golaced/Quadruped-Robot-Moco-12-/教程2-主机架设计/moco-8 Test Verison/侧摆电机.SLDPRT

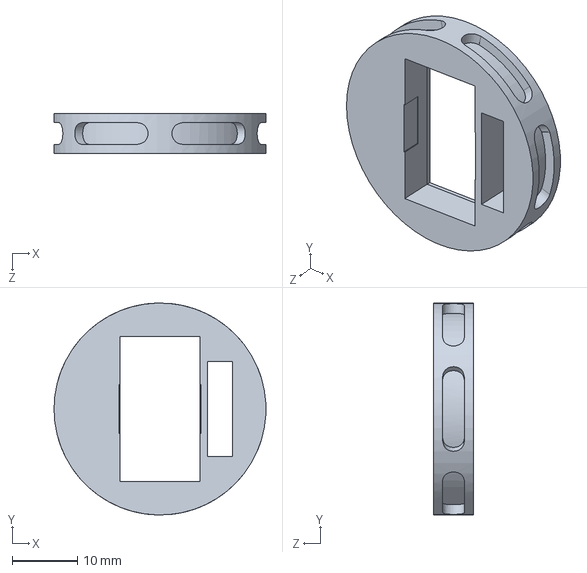
[picture p118: CAD file, 2020-06-26]
教程2-主机架设计/moco-8 Test Verison/侧摆电机.SLDPRT
32.5 x 32.5 x 6.13 mm
