golaced/Quadruped-Robot-Moco-12-/教程2-主机架设计/1.0 SW文件/开关支撑.SLDPRT

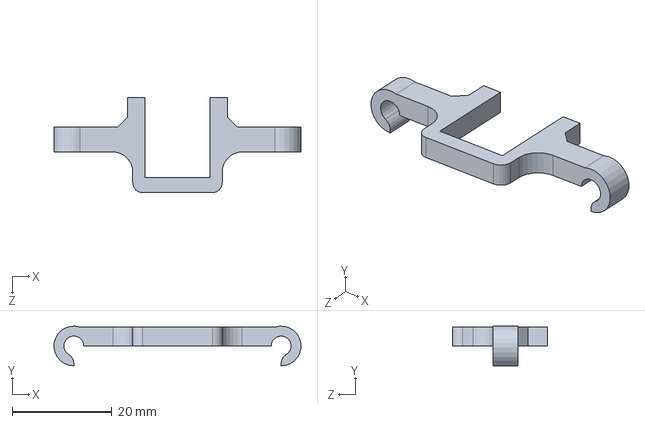
[picture p119: CAD file, 2020-02-27]
教程2-主机架设计/1.0 SW文件/开关支撑.SLDPRT
49.6 x 7.99 x 19.2 mm
