golaced/Quadruped-Robot-Moco-12-/教程2-主机架设计/1.2 版本加工文件/小腿杆 4个.SLDPRT

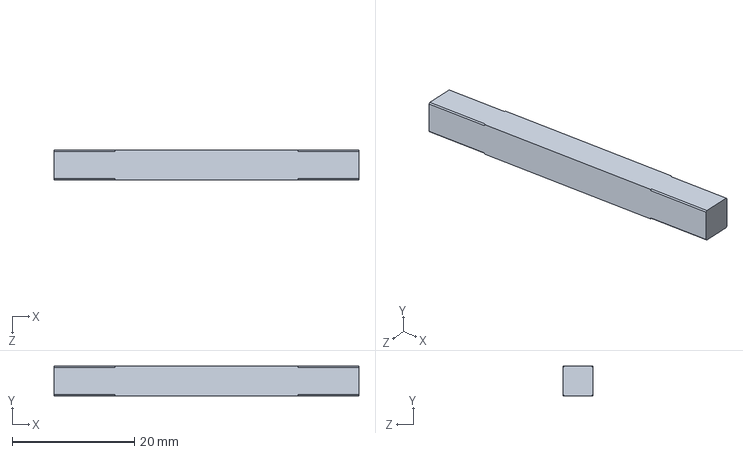
[picture p120: CAD file, 2020-06-15]
教程2-主机架设计/1.2 版本加工文件/小腿杆 4个.SLDPRT
50.0 x 4.85 x 4.85 mm
