golaced/Quadruped-Robot-Moco-12-/教程2-主机架设计/moco-8 Test Verison/大腿.SLDPRT

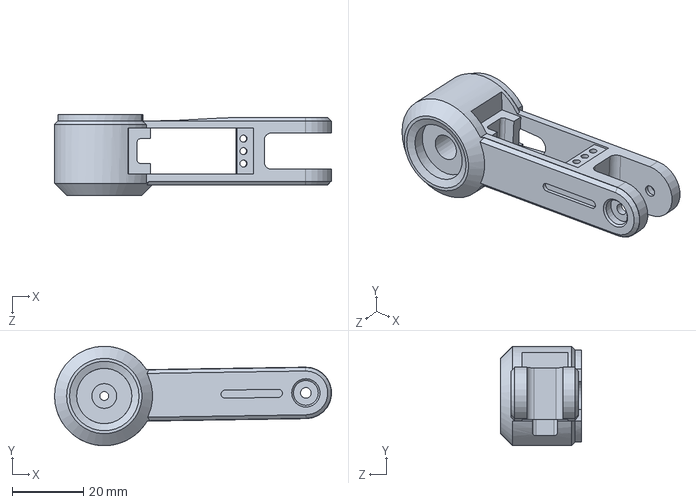
[picture p121: CAD file, 2020-06-26]
教程2-主机架设计/moco-8 Test Verison/大腿.SLDPRT
77.9 x 28.0 x 22.8 mm
