golaced/Quadruped-Robot-Moco-12-/教程2-主机架设计/1.0 SW文件/大腿_舵机保护.SLDPRT

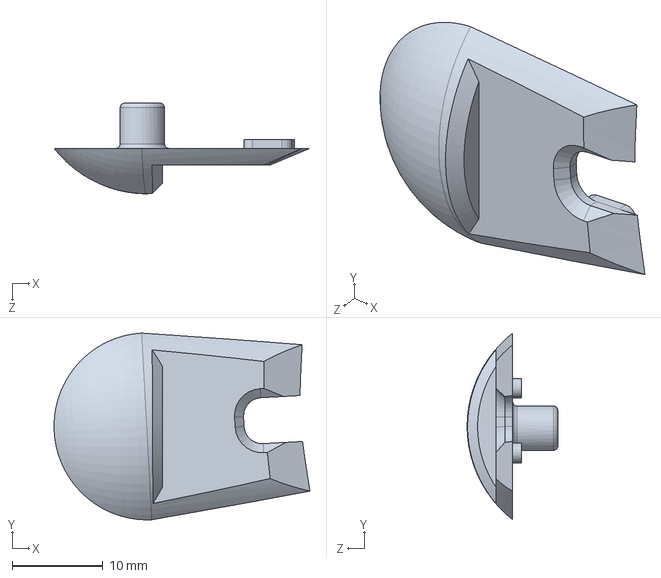
[picture p122: CAD file, 2020-02-27]
教程2-主机架设计/1.0 SW文件/大腿_舵机保护.SLDPRT
28.3 x 20.6 x 10.0 mm
