golaced/Quadruped-Robot-Moco-12-/教程2-主机架设计/moco-8 Test Verison/足底.SLDPRT

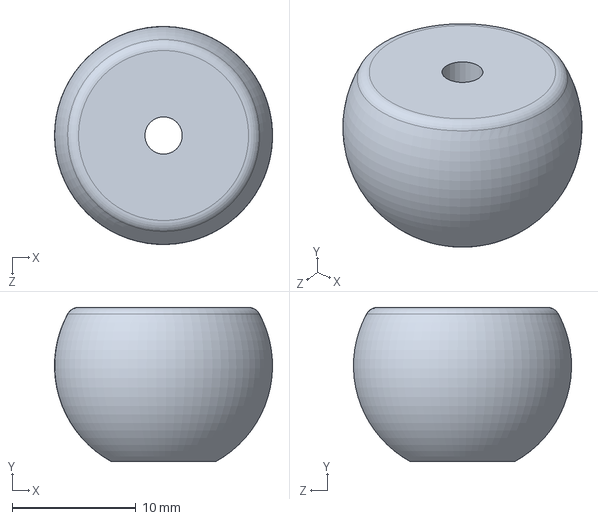
[picture p123: CAD file, 2020-06-26]
教程2-主机架设计/moco-8 Test Verison/足底.SLDPRT
17.6 x 12.4 x 17.6 mm
