golaced/Quadruped-Robot-Moco-12-/教程2-主机架设计/1.2 版本加工文件/侧挡板1 2个.SLDPRT

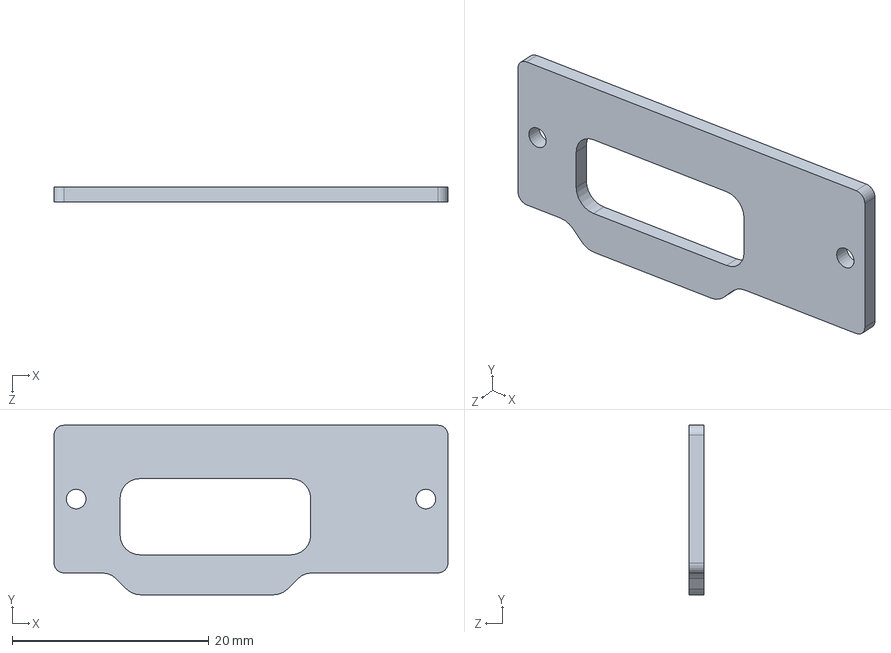
[picture p124: CAD file, 2020-06-15]
教程2-主机架设计/1.2 版本加工文件/侧挡板1 2个.SLDPRT
40.0 x 17.2 x 1.50 mm
