golaced/Quadruped-Robot-Moco-12-/教程2-主机架设计/1.0 SW文件/顶支架.SLDPRT

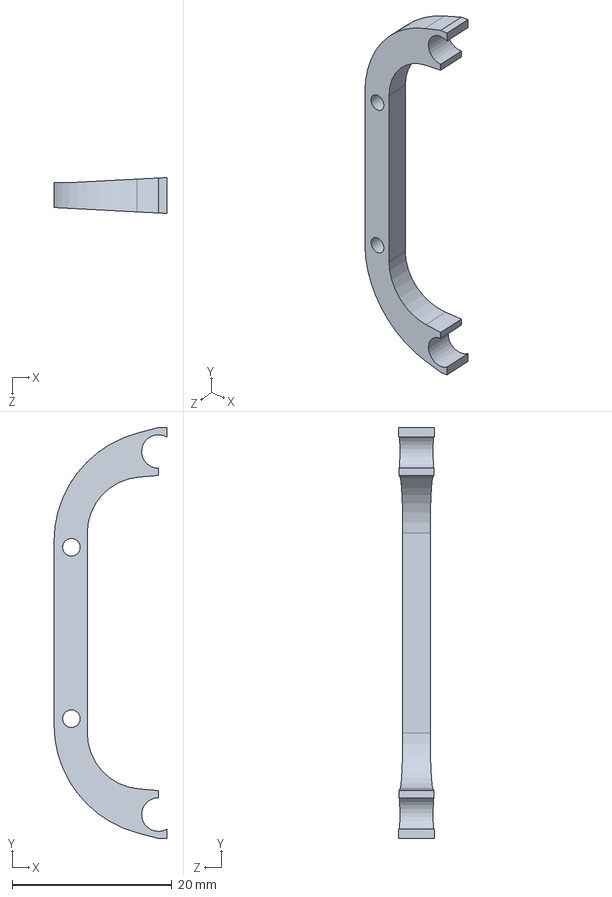
[picture p125: CAD file, 2020-02-27]
教程2-主机架设计/1.0 SW文件/顶支架.SLDPRT
14.1 x 51.5 x 4.50 mm
