golaced/Quadruped-Robot-Moco-12-/教程2-主机架设计/1.2 版本加工文件/侧挡板2 2个.SLDPRT

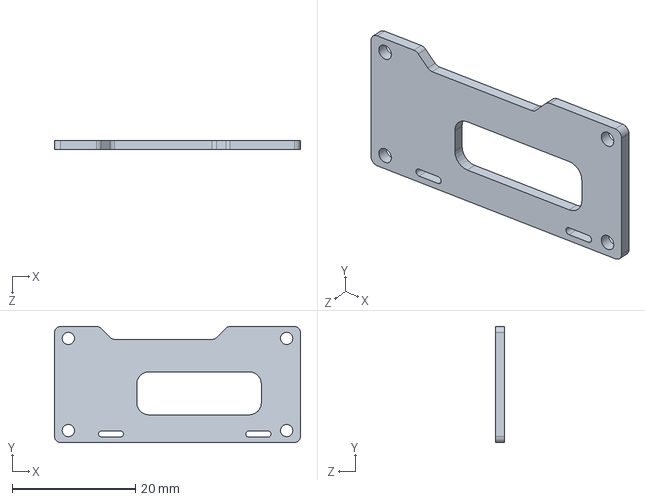
[picture p126: CAD file, 2020-06-15]
教程2-主机架设计/1.2 版本加工文件/侧挡板2 2个.SLDPRT
40.0 x 18.9 x 1.50 mm
