golaced/Quadruped-Robot-Moco-12-/教程2-主机架设计/1.0 SW文件/电池仓.SLDPRT

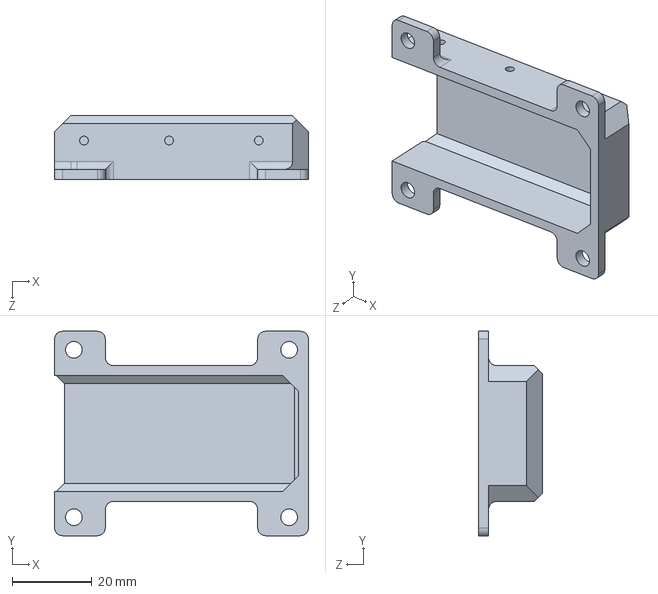
[picture p127: CAD file, 2020-02-27]
教程2-主机架设计/1.0 SW文件/电池仓.SLDPRT
63.7 x 51.3 x 16.0 mm
