golaced/Quadruped-Robot-Moco-12-/教程2-主机架设计/1.2 版本加工文件/控制器安装结构件 1个.SLDPRT

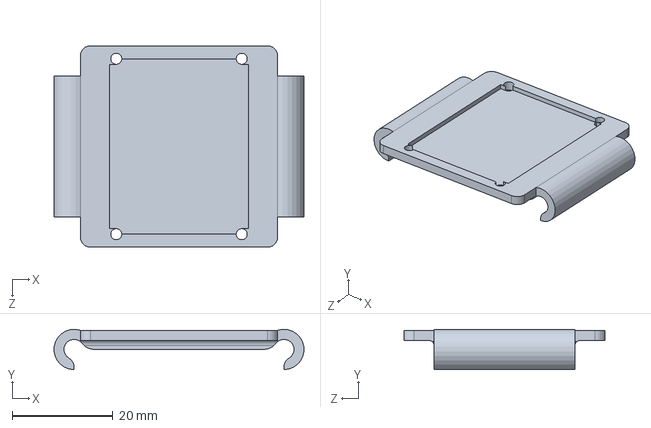
[picture p128: CAD file, 2020-06-15]
教程2-主机架设计/1.2 版本加工文件/控制器安装结构件 1个.SLDPRT
49.6 x 7.99 x 40.0 mm
