golaced/Quadruped-Robot-Moco-12-/教程2-主机架设计/moco-8 Test Verison/顶盖.SLDPRT

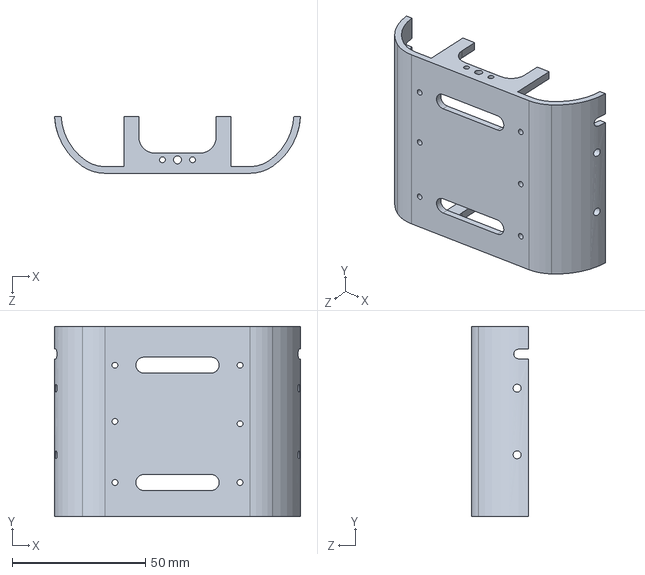
[picture p129: CAD file, 2020-06-26]
教程2-主机架设计/moco-8 Test Verison/顶盖.SLDPRT
92.3 x 71.4 x 21.2 mm
