golaced/Quadruped-Robot-Moco-12-/教程2-主机架设计/1.0 SW文件/跨舵机固定双.SLDPRT

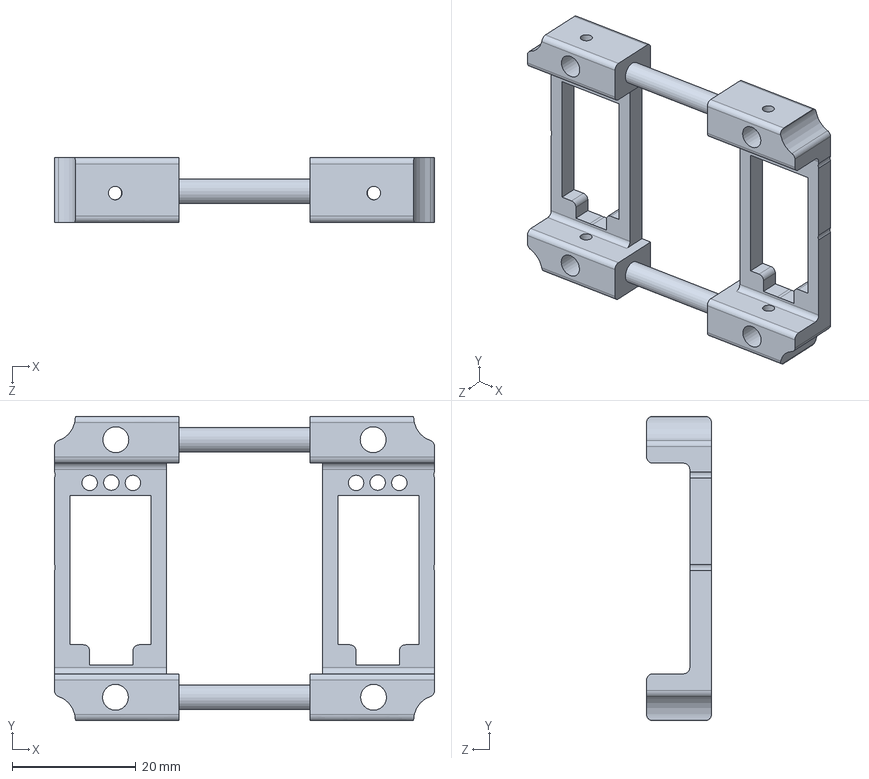
[picture p130: CAD file, 2020-02-27]
教程2-主机架设计/1.0 SW文件/跨舵机固定双.SLDPRT
61.5 x 49.3 x 10.5 mm
