golaced/Quadruped-Robot-Moco-12-/教程2-主机架设计/1.2 版本加工文件/顶部把手 2个.SLDPRT

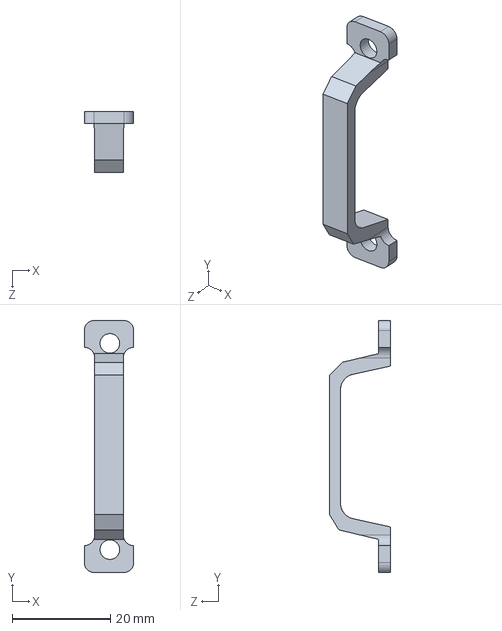
[picture p131: CAD file, 2020-06-15]
教程2-主机架设计/1.2 版本加工文件/顶部把手 2个.SLDPRT
10.1 x 51.3 x 12.5 mm
