golaced/Quadruped-Robot-Moco-12-/教程2-主机架设计/moco-8 Test Verison/小腿.SLDPRT

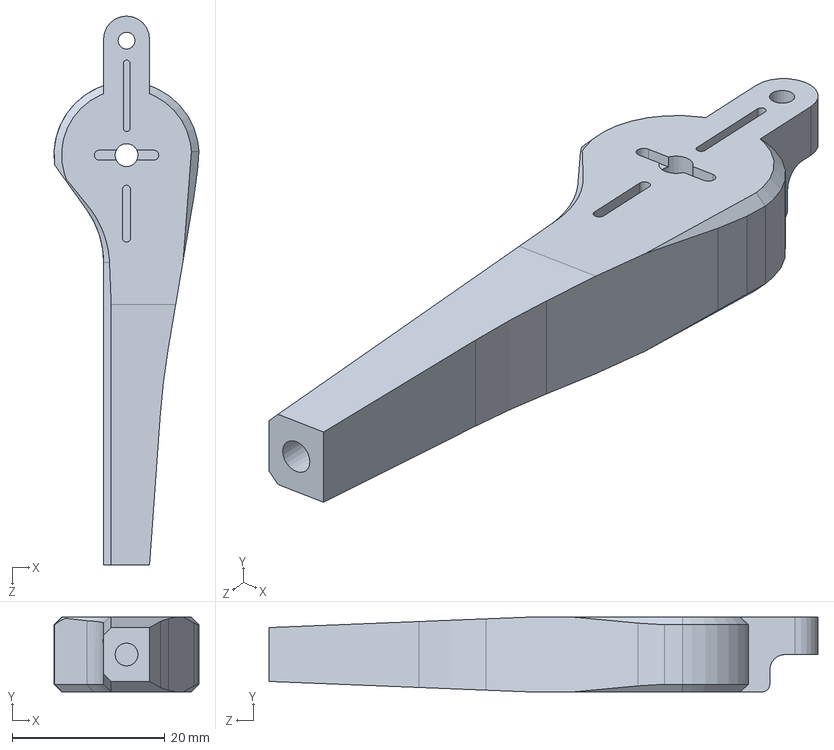
[picture p132: CAD file, 2020-06-26]
教程2-主机架设计/moco-8 Test Verison/小腿.SLDPRT
19.0 x 9.80 x 71.9 mm
