golaced/Quadruped-Robot-Moco-12-/教程2-主机架设计/1.2 版本加工文件/侧摆电机固定件 4个.SLDPRT

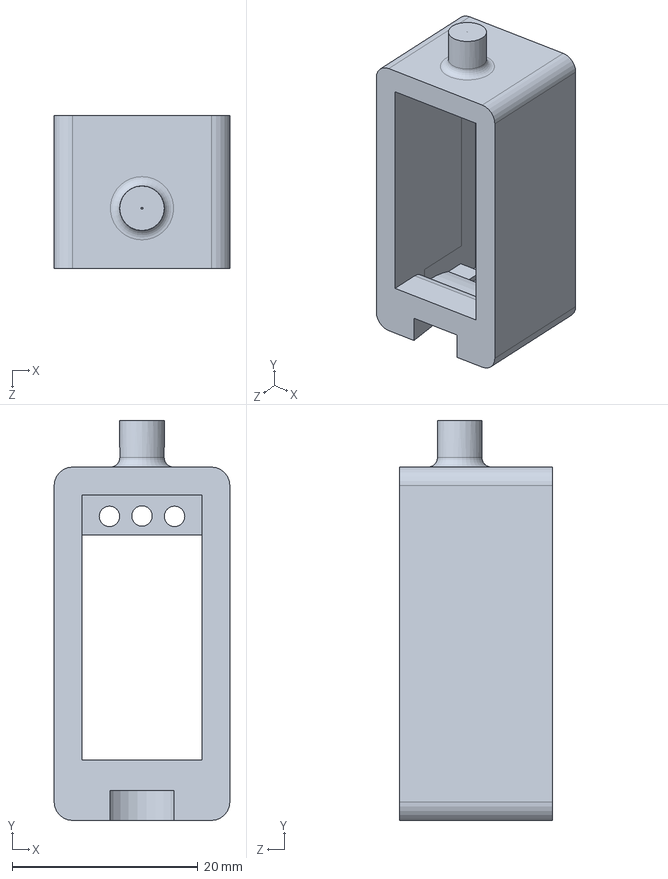
[picture p133: CAD file, 2020-06-15]
教程2-主机架设计/1.2 版本加工文件/侧摆电机固定件 4个.SLDPRT
18.9 x 43.0 x 16.5 mm
