golaced/Quadruped-Robot-Moco-12-/教程2-主机架设计/moco-8 Test Verison/机架.SLDPRT

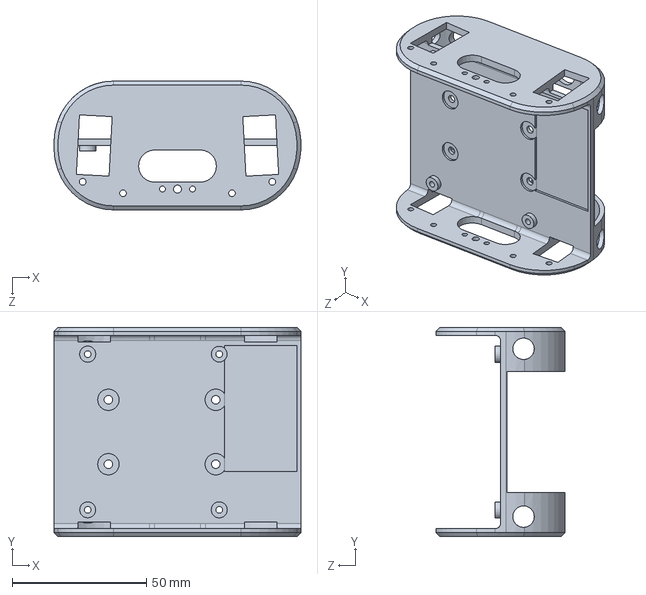
[picture p134: CAD file, 2020-06-26]
教程2-主机架设计/moco-8 Test Verison/机架.SLDPRT
92.0 x 78.0 x 48.0 mm
