golaced/Quadruped-Robot-Moco-12-/教程2-主机架设计/1.0 SW文件/小腿连杆固定1.SLDPRT

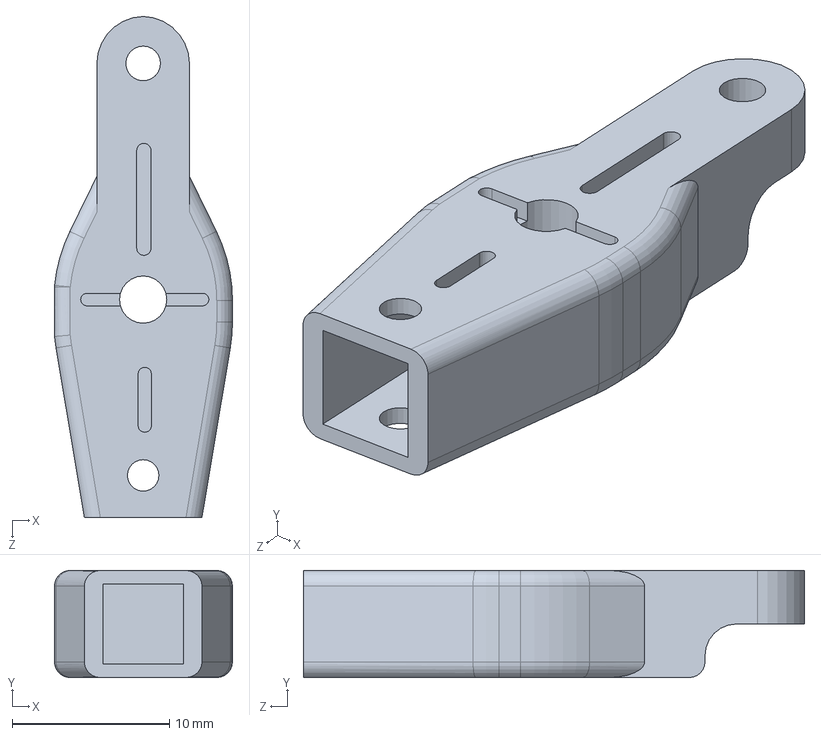
[picture p135: CAD file, 2020-02-27]
教程2-主机架设计/1.0 SW文件/小腿连杆固定1.SLDPRT
11.3 x 6.80 x 31.8 mm
