golaced/Quadruped-Robot-Moco-12-/教程2-主机架设计/1.2 版本加工文件/大腿结构件（左右侧腿镜像打印 各2个）.SLDPRT

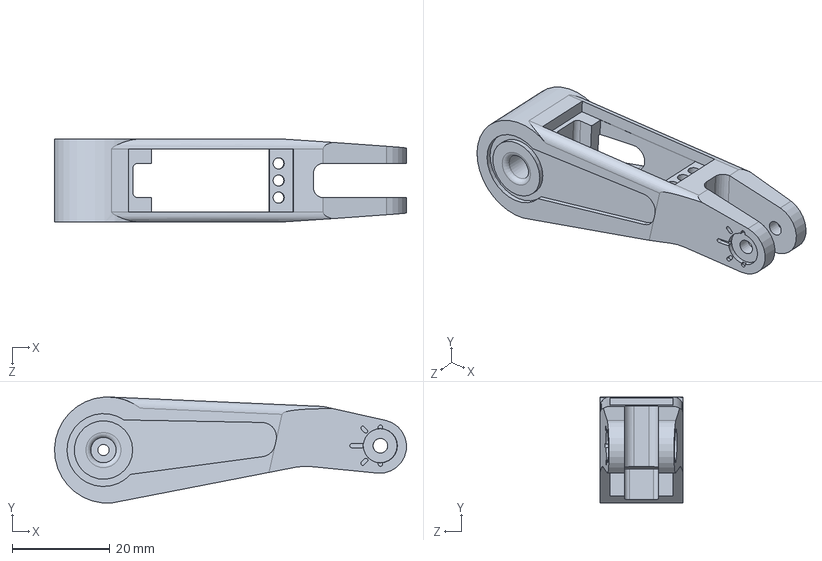
[picture p136: CAD file, 2020-06-15]
教程2-主机架设计/1.2 版本加工文件/大腿结构件（左右侧腿镜像打印 各2个）.SLDPRT
72.1 x 21.7 x 17.0 mm
