golaced/Quadruped-Robot-Moco-12-/教程2-主机架设计/moco-8 Test Verison/足底固定.SLDPRT

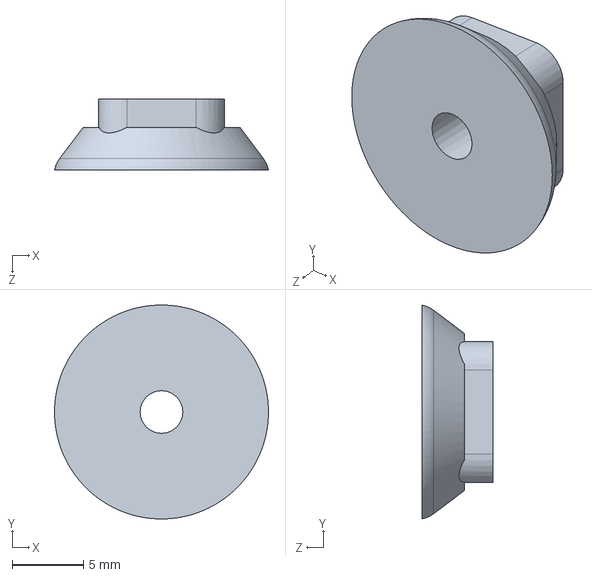
[picture p137: CAD file, 2020-06-26]
教程2-主机架设计/moco-8 Test Verison/足底固定.SLDPRT
15.0 x 15.0 x 5.00 mm
