golaced/Quadruped-Robot-Moco-12-/教程2-主机架设计/1.0 SW文件/侧支架.SLDPRT

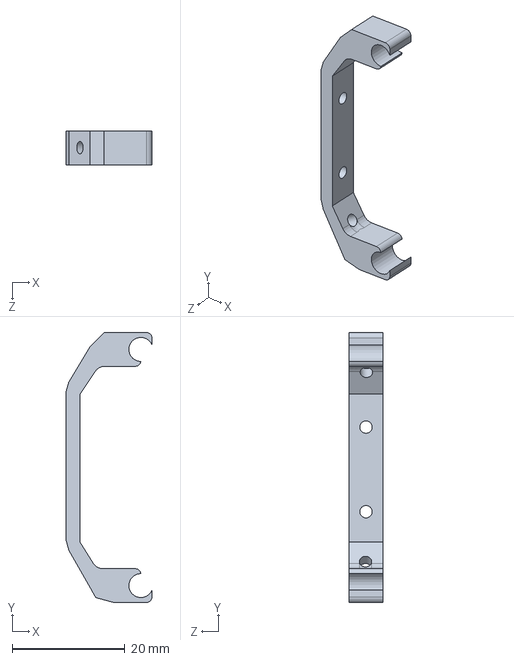
[picture p138: CAD file, 2020-02-27]
教程2-主机架设计/1.0 SW文件/侧支架.SLDPRT
15.3 x 47.9 x 6.00 mm
