golaced/Quadruped-Robot-Moco-12-/教程2-主机架设计/moco-8 Test Verison/电池.SLDPRT

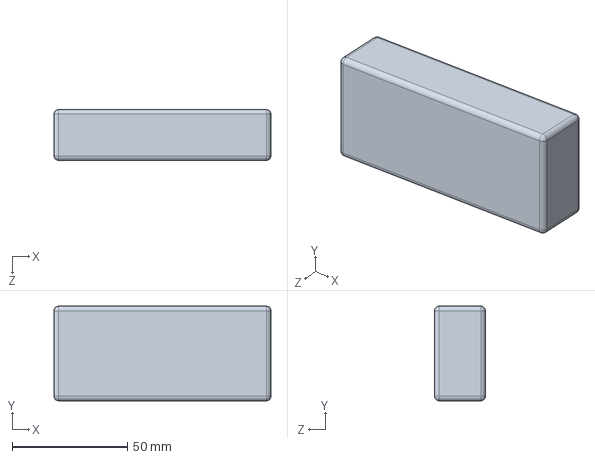
[picture p139: CAD file, 2020-06-26]
教程2-主机架设计/moco-8 Test Verison/电池.SLDPRT
94.0 x 41.0 x 22.0 mm
