golaced/Quadruped-Robot-Moco-12-/教程2-主机架设计/moco-8 Test Verison/大腿固定.SLDPRT

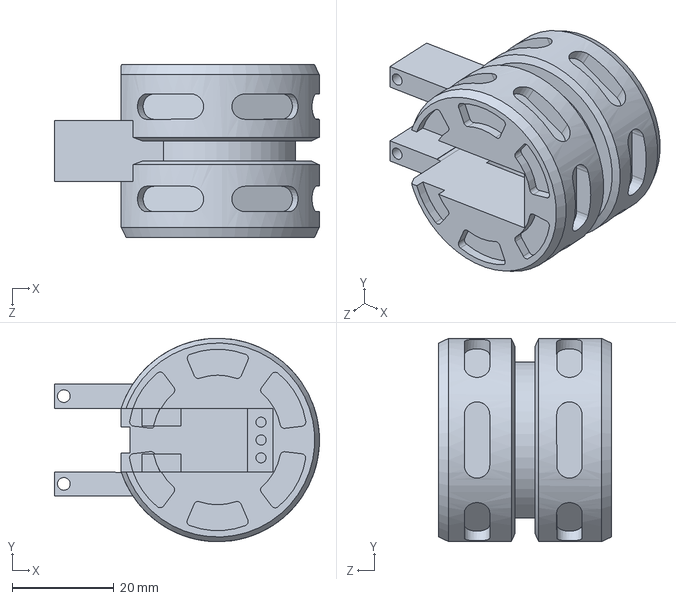
[picture p140: CAD file, 2020-06-26]
教程2-主机架设计/moco-8 Test Verison/大腿固定.SLDPRT
52.1 x 40.0 x 34.0 mm
