golaced/Quadruped-Robot-Moco-12-/教程2-主机架设计/moco-8 Test Verison/尾巴.SLDPRT

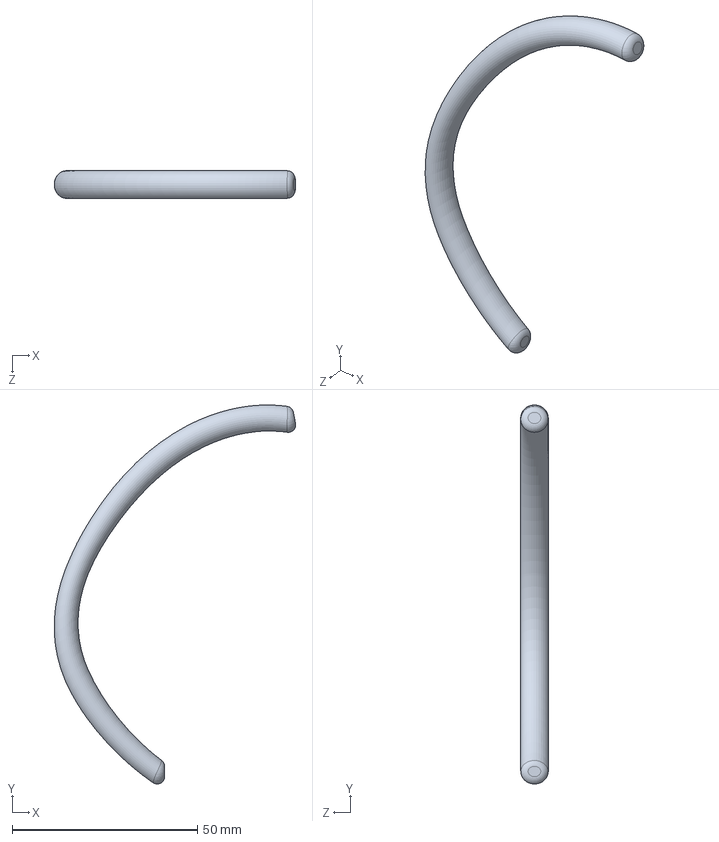
[picture p141: CAD file, 2020-06-26]
教程2-主机架设计/moco-8 Test Verison/尾巴.SLDPRT
65.2 x 102.4 x 7.45 mm
