golaced/Quadruped-Robot-Moco-12-/教程2-主机架设计/moco-8 Test Verison/9g舵机.SLDPRT

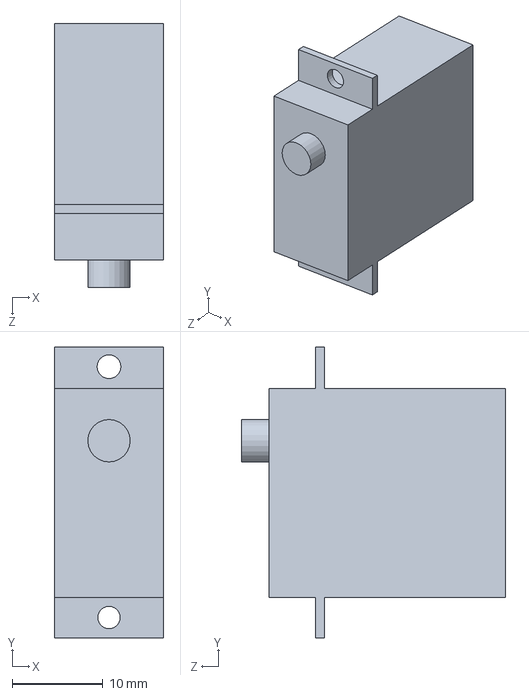
[picture p142: CAD file, 2020-02-07]
教程2-主机架设计/moco-8 Test Verison/9g舵机.SLDPRT
12.0 x 32.0 x 29.0 mm
