golaced/Quadruped-Robot-Moco-12-/教程2-主机架设计/1.2 版本加工文件/5 10 4 法兰.SLDPRT

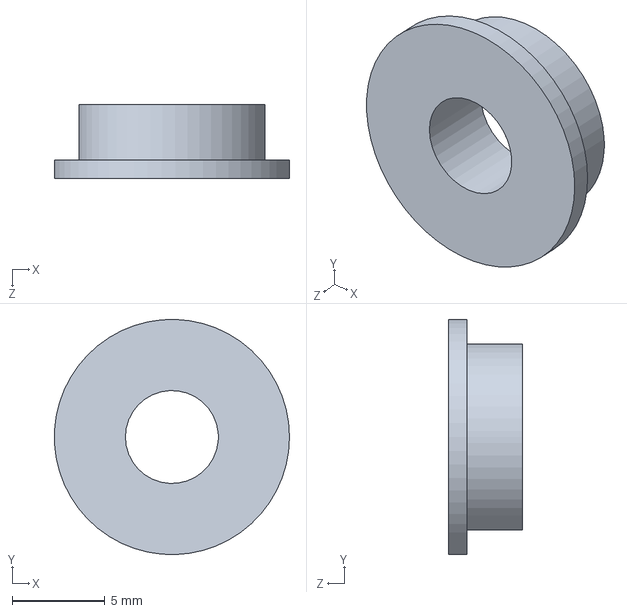
[picture p143: CAD file, 2020-02-07]
教程2-主机架设计/1.2 版本加工文件/5 10 4 法兰.SLDPRT
12.6 x 12.6 x 4.00 mm
