golaced/Quadruped-Robot-Moco-12-/教程2-主机架设计/1.0 SW文件/风扇.SLDPRT

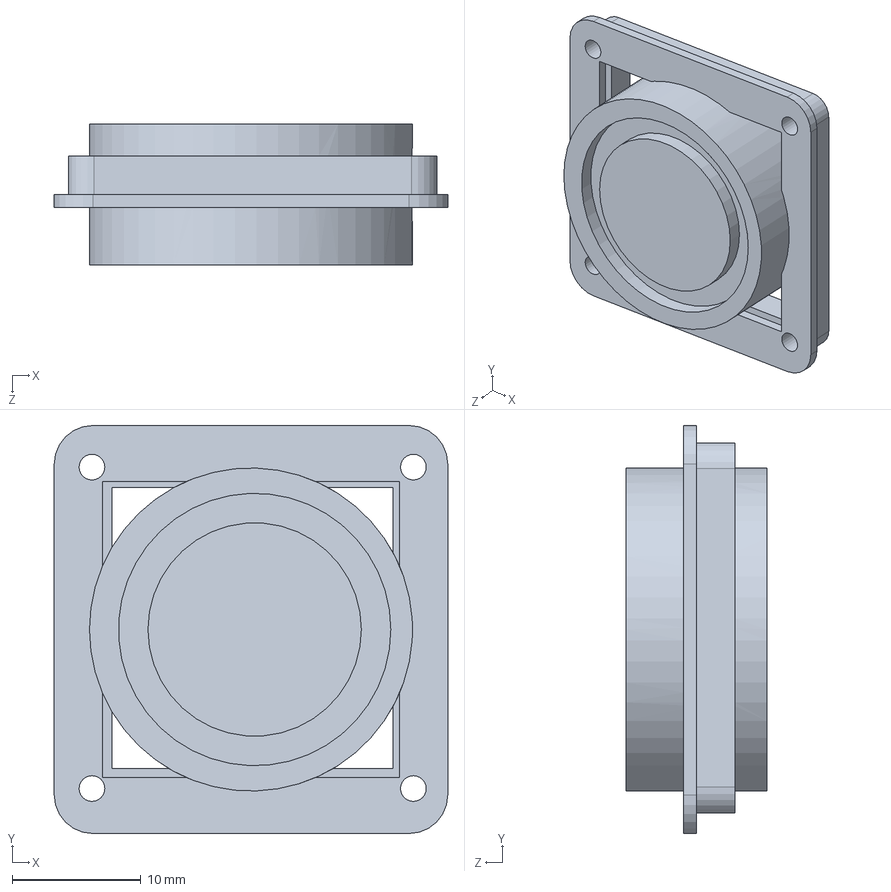
[picture p144: CAD file, 2020-02-07]
教程2-主机架设计/1.0 SW文件/风扇.SLDPRT
30.6 x 31.7 x 11.0 mm
