golaced/Quadruped-Robot-Moco-12-/教程2-主机架设计/1.2 版本加工文件/摇臂1.SLDPRT

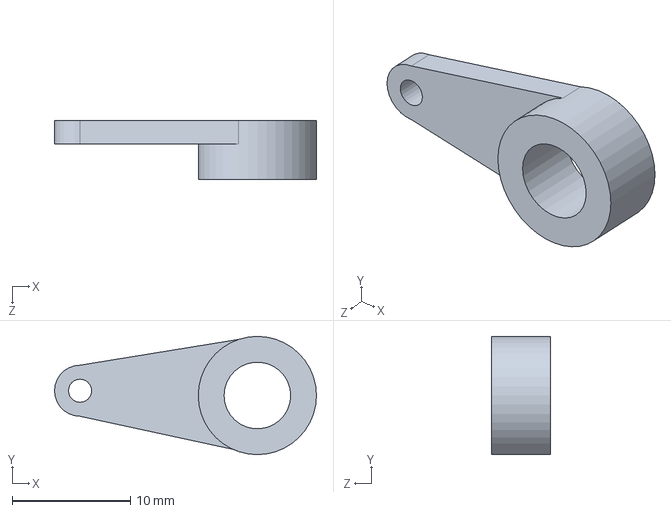
[picture p145: CAD file, 2020-02-07]
教程2-主机架设计/1.2 版本加工文件/摇臂1.SLDPRT
22.2 x 10.00 x 5.00 mm
