golaced/Quadruped-Robot-Moco-12-/教程2-主机架设计/1.2 版本加工文件/足底 4个.SLDPRT

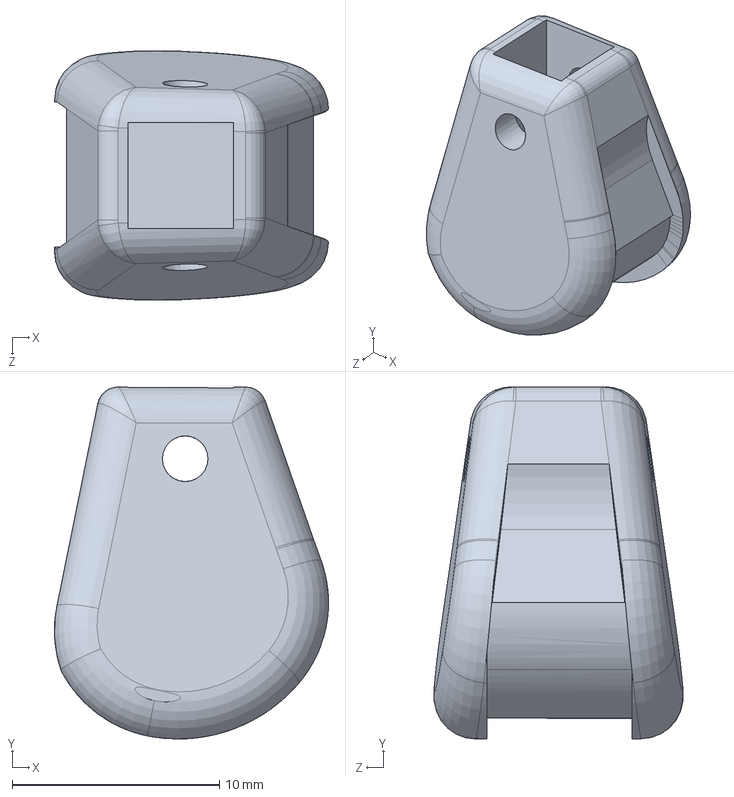
[picture p146: CAD file, 2020-02-07]
教程2-主机架设计/1.2 版本加工文件/足底 4个.SLDPRT
13.2 x 17.0 x 12.0 mm
