golaced/Quadruped-Robot-Moco-12-/教程2-主机架设计/1.0 SW文件/三通1.SLDPRT

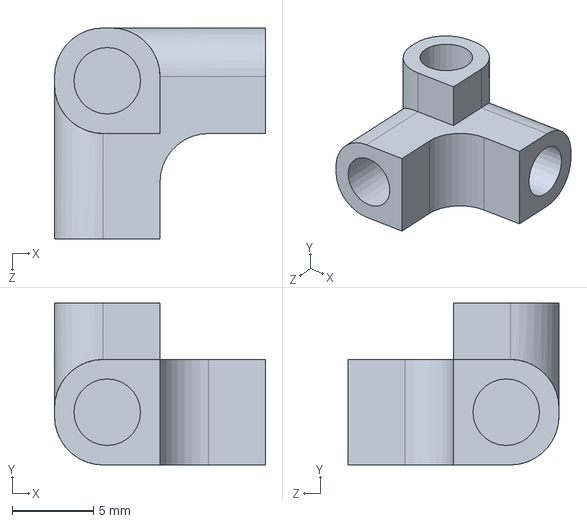
[picture p147: CAD file, 2020-02-07]
教程2-主机架设计/1.0 SW文件/三通1.SLDPRT
13.0 x 9.98 x 13.0 mm
