golaced/Quadruped-Robot-Moco-12-/教程2-主机架设计/1.2 版本加工文件/主机架碳管.SLDPRT

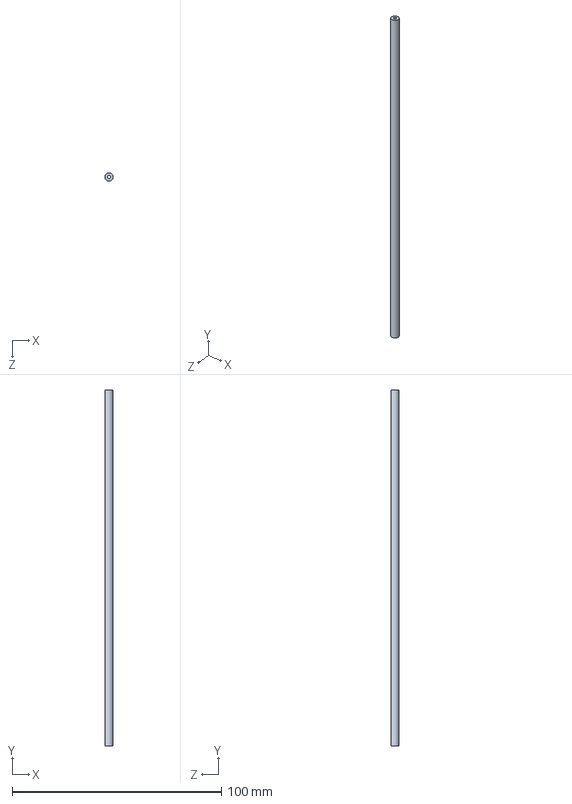
[picture p148: CAD file, 2020-02-07]
教程2-主机架设计/1.2 版本加工文件/主机架碳管.SLDPRT
4.00 x 170.0 x 4.00 mm
