golaced/Quadruped-Robot-Moco-12-/教程2-主机架设计/1.0 SW文件/大腿圆盘固定.SLDPRT

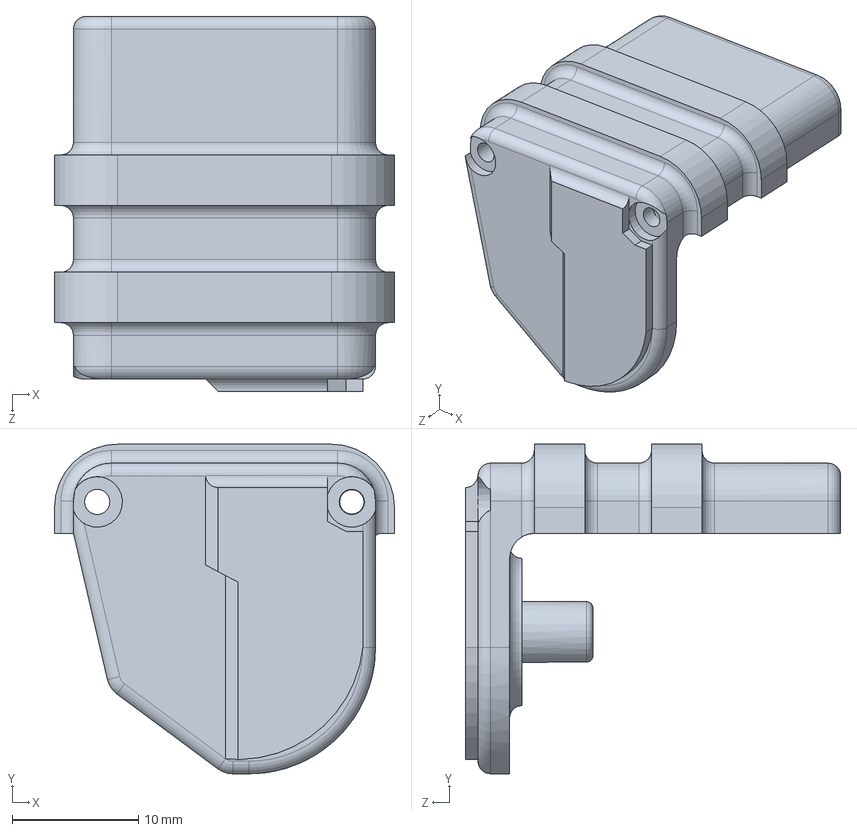
[picture p149: CAD file, 2020-02-07]
教程2-主机架设计/1.0 SW文件/大腿圆盘固定.SLDPRT
26.9 x 26.1 x 29.7 mm
