golaced/Quadruped-Robot-Moco-12-/教程2-主机架设计/1.0 SW文件/大腿圆盘固定长.SLDPRT

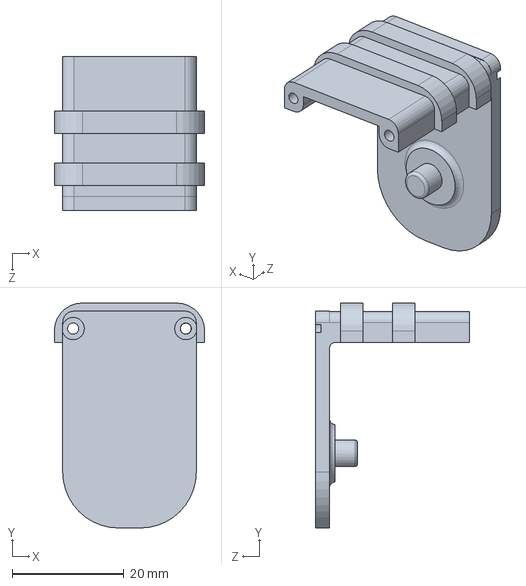
[picture p150: CAD file, 2020-02-07]
教程2-主机架设计/1.0 SW文件/大腿圆盘固定长.SLDPRT
26.9 x 40.2 x 27.5 mm
