golaced/Quadruped-Robot-Moco-12-/教程2-主机架设计/1.0 SW文件/机架杆2.SLDPRT

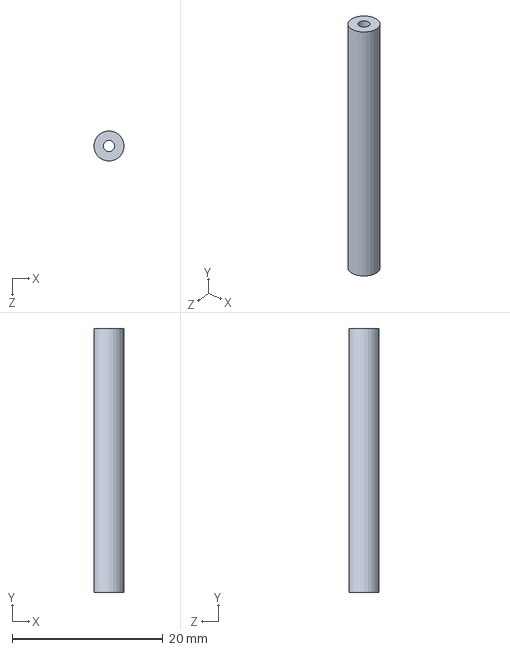
[picture p151: CAD file, 2020-02-07]
教程2-主机架设计/1.0 SW文件/机架杆2.SLDPRT
4.00 x 35.0 x 4.00 mm
