golaced/Quadruped-Robot-Moco-12-/教程2-主机架设计/1.0 SW文件/大腿舵机固定.SLDPRT

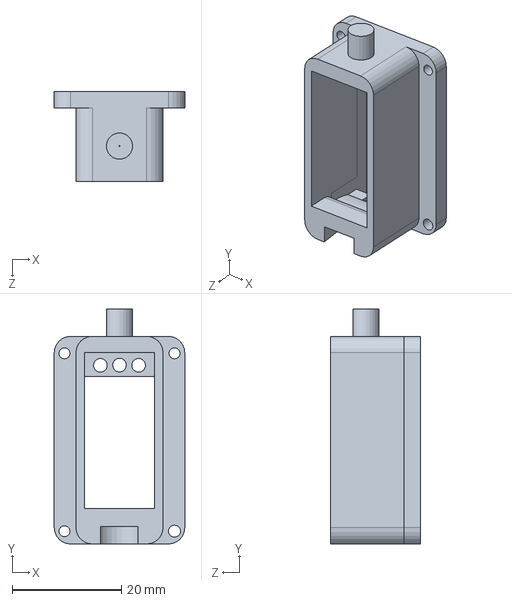
[picture p152: CAD file, 2020-02-07]
教程2-主机架设计/1.0 SW文件/大腿舵机固定.SLDPRT
23.9 x 43.0 x 16.5 mm
