golaced/Quadruped-Robot-Moco-12-/教程2-主机架设计/1.0 SW文件/跨舵机固定.SLDPRT

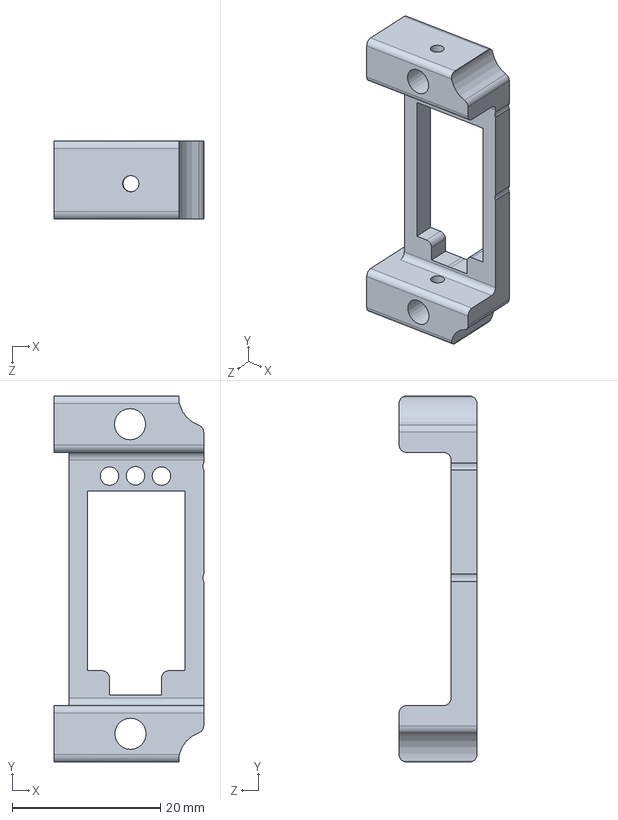
[picture p153: CAD file, 2020-02-07]
教程2-主机架设计/1.0 SW文件/跨舵机固定.SLDPRT
20.1 x 49.3 x 10.5 mm
