golaced/Quadruped-Robot-Moco-12-/教程2-主机架设计/1.0 SW文件/大腿圆盘固定1.SLDPRT

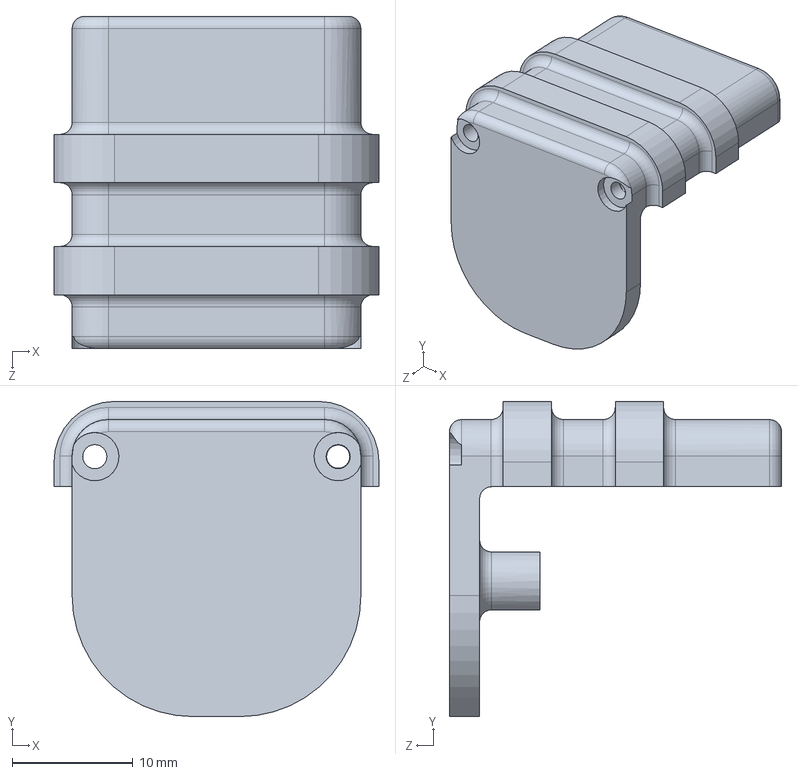
[picture p154: CAD file, 2020-02-07]
教程2-主机架设计/1.0 SW文件/大腿圆盘固定1.SLDPRT
26.9 x 26.1 x 27.5 mm
