golaced/Quadruped-Robot-Moco-12-/教程2-主机架设计/1.0 SW文件/跨固定1.SLDPRT

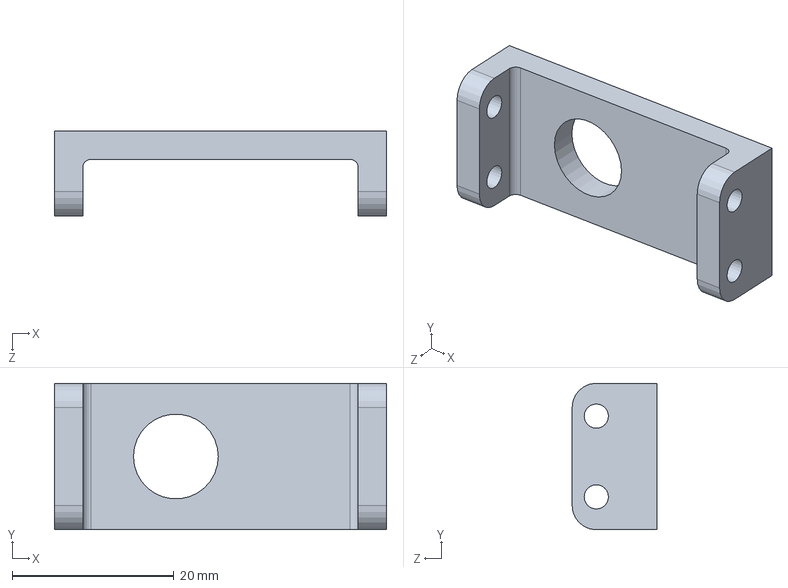
[picture p155: CAD file, 2020-02-07]
教程2-主机架设计/1.0 SW文件/跨固定1.SLDPRT
41.1 x 18.1 x 10.5 mm
