golaced/Quadruped-Robot-Moco-12-/教程2-主机架设计/1.0 SW文件/三通.SLDPRT

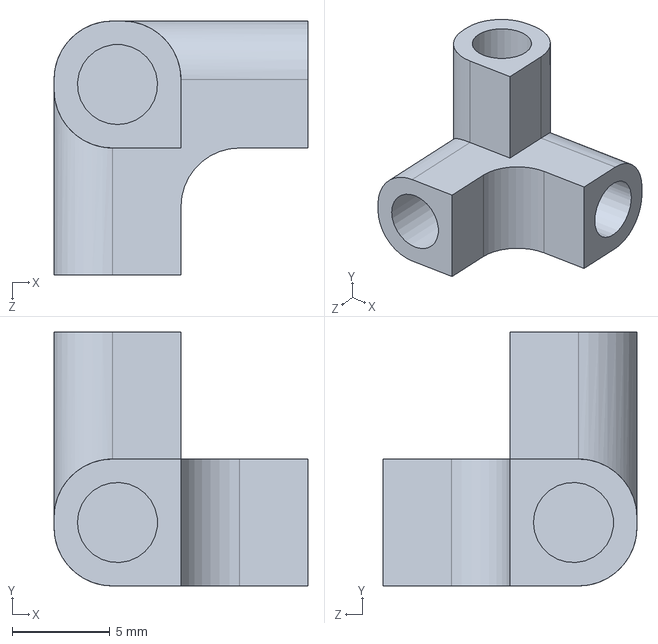
[picture p156: CAD file, 2020-02-07]
教程2-主机架设计/1.0 SW文件/三通.SLDPRT
13.0 x 13.0 x 13.0 mm
