golaced/Quadruped-Robot-Moco-12-/教程2-主机架设计/1.0 SW文件/跨固定2.SLDPRT

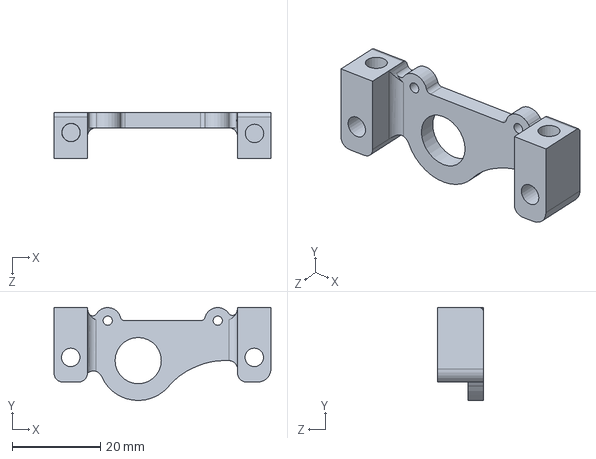
[picture p157: CAD file, 2020-02-07]
教程2-主机架设计/1.0 SW文件/跨固定2.SLDPRT
49.3 x 21.1 x 10.5 mm
