golaced/Quadruped-Robot-Moco-12-/教程2-主机架设计/1.0 SW文件/连杆固定.SLDPRT

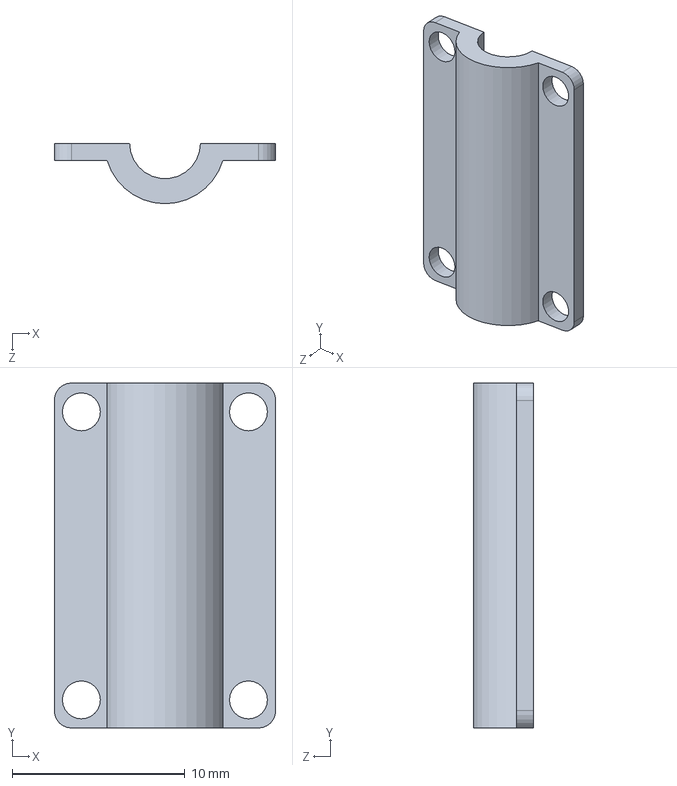
[picture p158: CAD file, 2020-02-07]
教程2-主机架设计/1.0 SW文件/连杆固定.SLDPRT
12.8 x 20.0 x 3.50 mm
