golaced/Quadruped-Robot-Moco-12-/教程2-主机架设计/moco-8 Test Verison/设计图/1.JPG

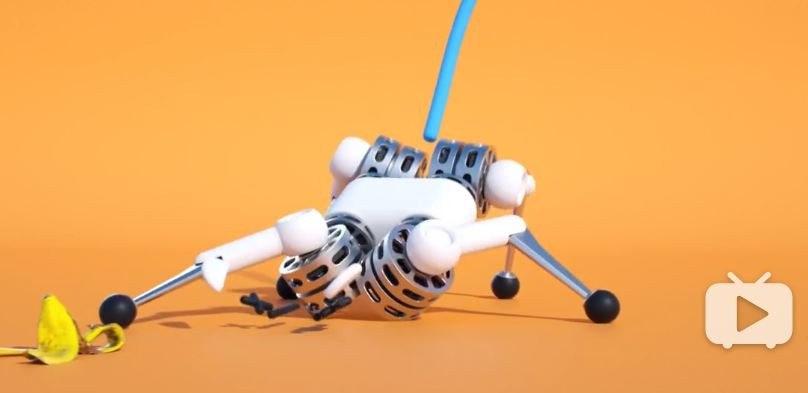
教程2-主机架设计/moco-8 Test Verison/设计图/1.JPG
